LenweSaralonde/musician-midi-pico-translator/raspberry-pi-pico-midi-shield.kicad_sch

## KiCad design raspberry-pi-pico-midi-shield.kicad_sch (2026-05-02)

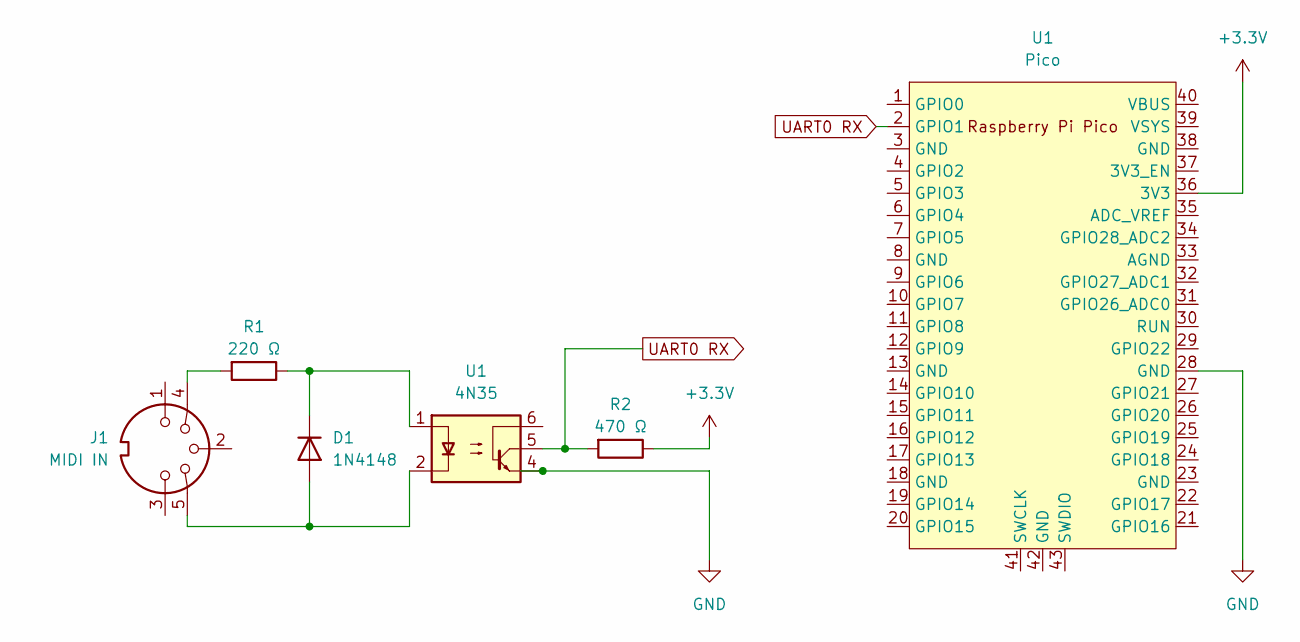
[picture p4: schematic raspberry-pi-pico-midi-shield.kicad_sch]

Parts:
D1: 1N4148; D_DO-35_SOD27_P7.62mm_Horizontal
J1: MIDI IN
R1: 220 Ω
R2: 470 Ω
U1: Pico; RPi_Pico_SMD_TH

Connections:
+3.3V: R2.1, U1.36 (3V3)
GND: U1.4, U1.28 (GND)
unnamed: D1.1 (K), R1.1, U1.1
unnamed: D1.2 (A), J1.5, U1.2
unnamed: J1.4, R1.2
UART0 RX: R2.2, U1.2, U1.5
